thingSoC/TSOC_GROVEY_WIFI/TSOC_GROVEY_WIFI/eagleUp/eagleUp_TSOC_GROVEY_WIFI_board_bottom.jpg

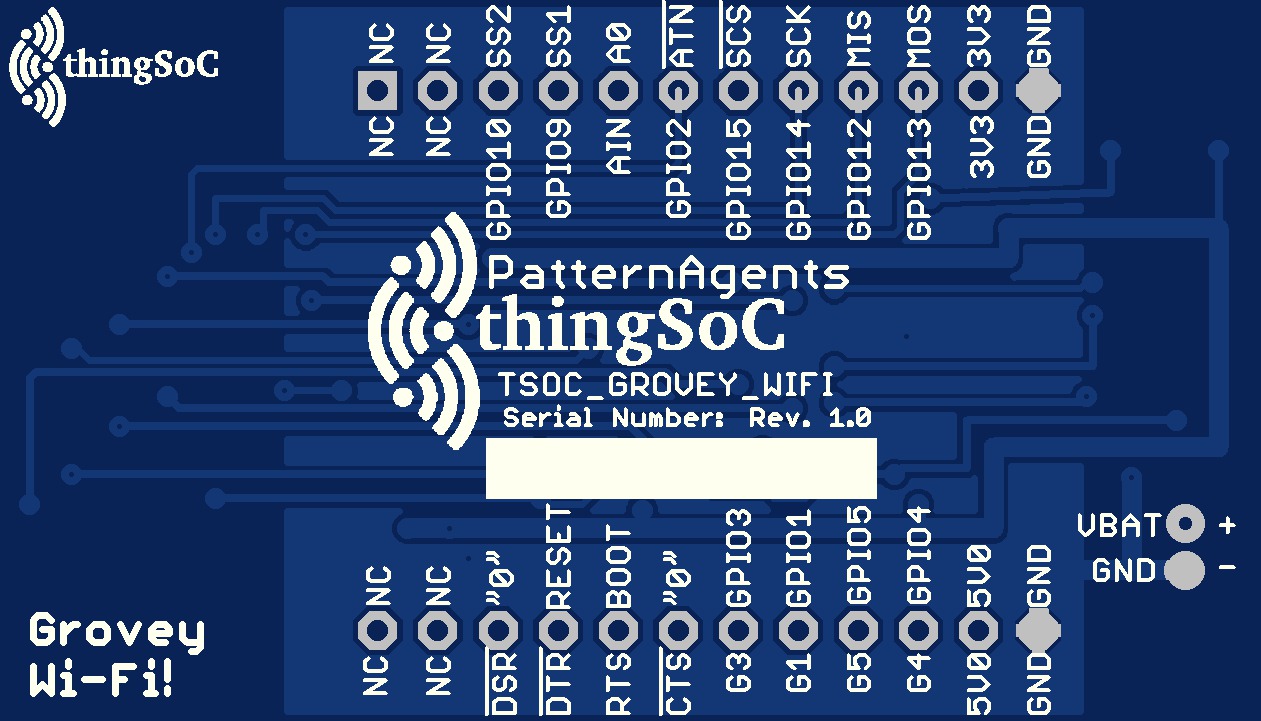
TSOC_GROVEY_WIFI/eagleUp/eagleUp_TSOC_GROVEY_WIFI_board_bottom.jpg
