thingSoC/TSOC_GROVEY_WIFI/TSOC_GROVEY_WIFI/images/TSOC_GROVEY_WIFI_iso.png

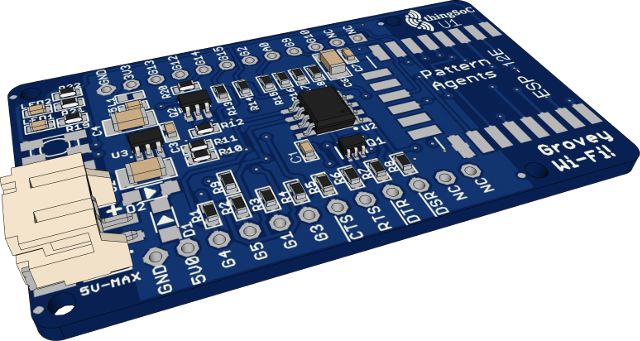
TSOC_GROVEY_WIFI/images/TSOC_GROVEY_WIFI_iso.png
